maxisimonazzi/Azukar-FPGA/docs/pinout/Pinout Azukar v2 (transparente).png

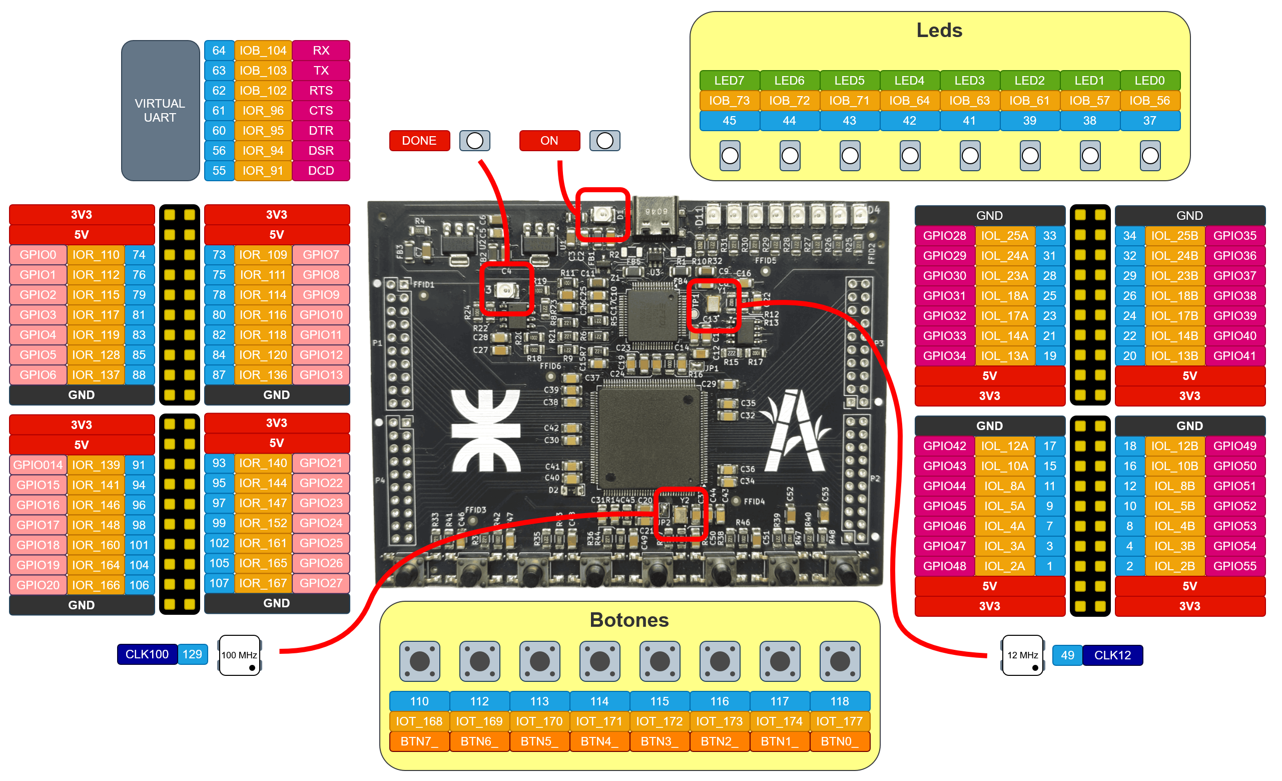
docs/pinout/Pinout Azukar v2 (transparente).png
