maxisimonazzi/Azukar-FPGA/images/3d/azukar-back.png

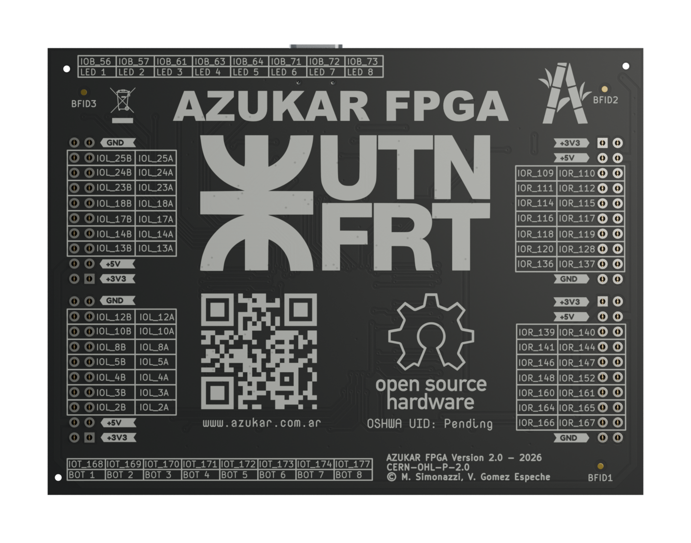
images/3d/azukar-back.png
