maxisimonazzi/Azukar-FPGA/images/3d/azukar-front.png

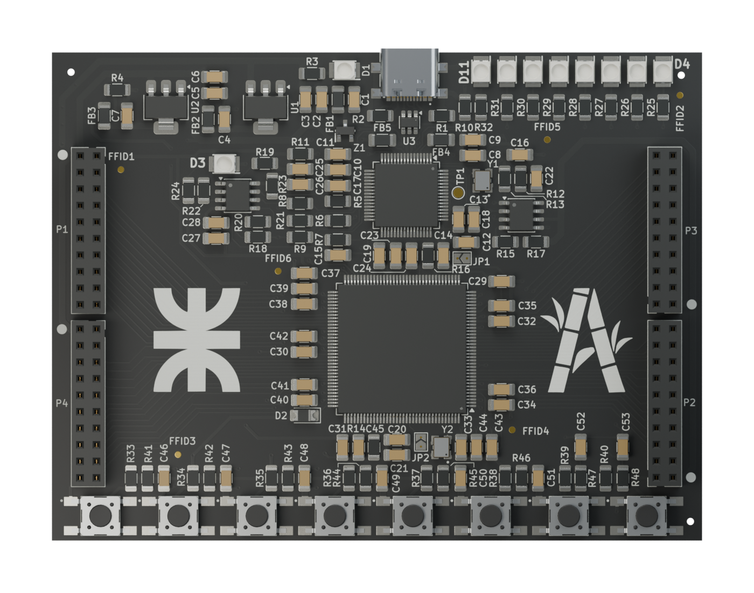
images/3d/azukar-front.png
