maxisimonazzi/Azukar-FPGA/images/3d/azukar-front.webp

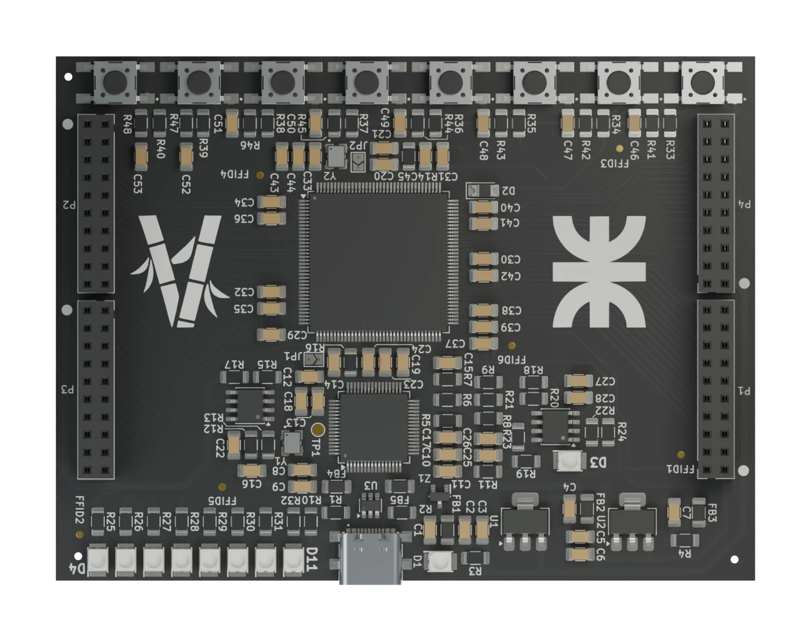
images/3d/azukar-front.webp
