maxisimonazzi/Azukar-FPGA/images/3d/azukar-hero.png

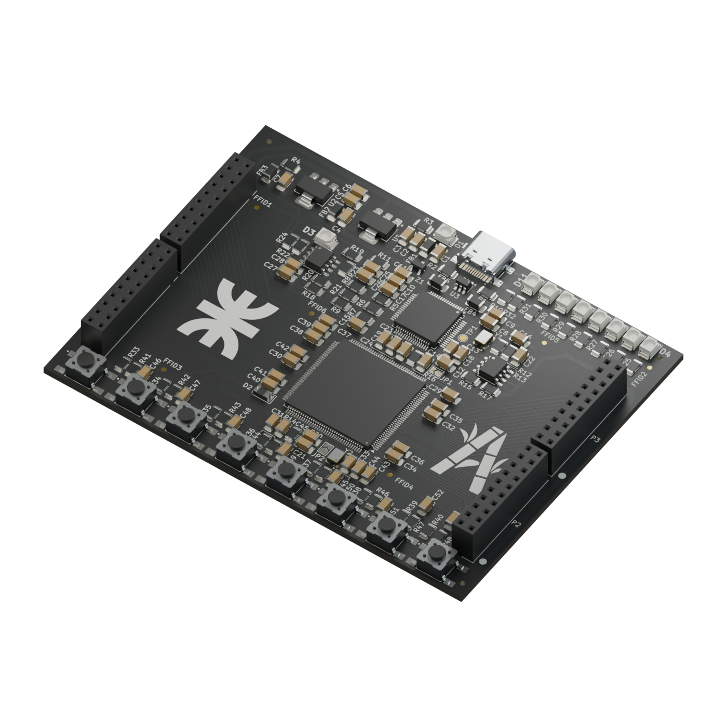
images/3d/azukar-hero.png
