maxisimonazzi/Azukar-FPGA/images/FPGA diagrama de bloques.png

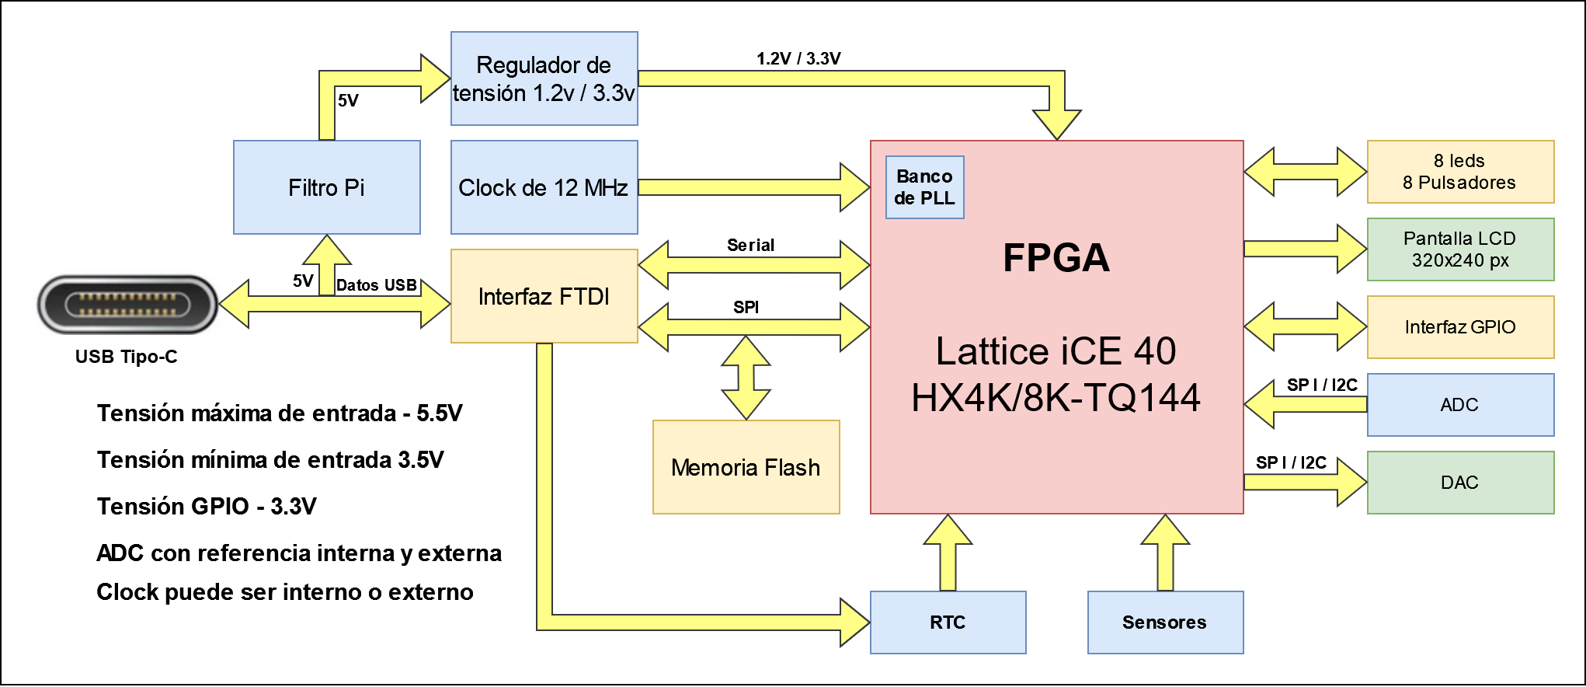
images/FPGA diagrama de bloques.png
